liffiton/ATLeS/designs/dist/end1.dxf

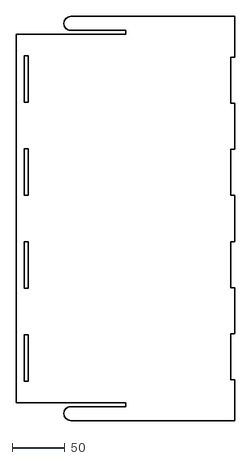
[picture p20: CAD file, 2017-09-16]
designs/dist/end1.dxf
206.0 x 381.5
