liffiton/ATLeS/designs/dist/tank_baffle_for_shock.dxf

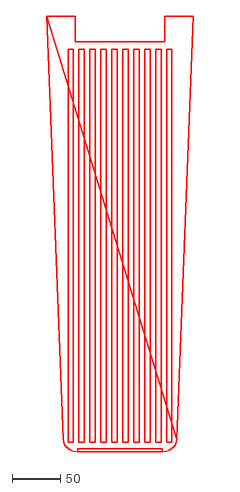
[picture p21: CAD file, 2017-09-08]
designs/dist/tank_baffle_for_shock.dxf
152.8 x 453.3
