liffiton/ATLeS/designs/dist/tank_baffle.dxf

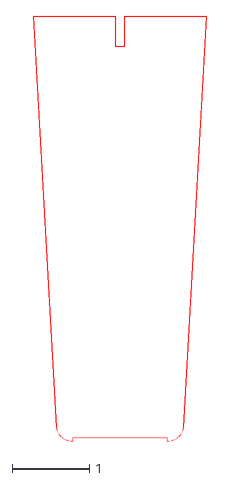
[picture p22: CAD file, 2016-03-01]
designs/dist/tank_baffle.dxf
2.24 x 5.51
