liffiton/ATLeS/designs/old/cut_test2.dxf

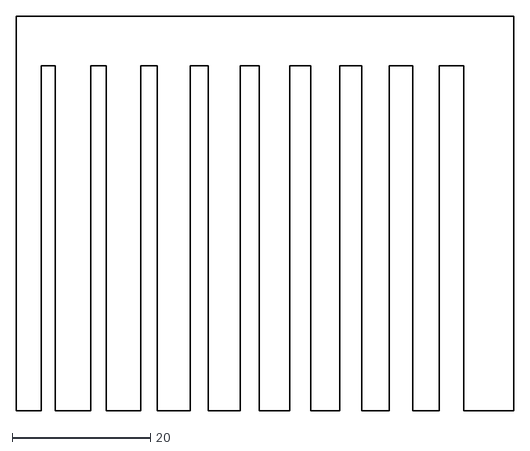
[picture p23: CAD file, 2016-03-01, an earlier design]
designs/old/cut_test2.dxf
72.0 x 57.2
